Nordln/Customizable-Boot-Camper-Box/20211127_095921_Medium.jpg

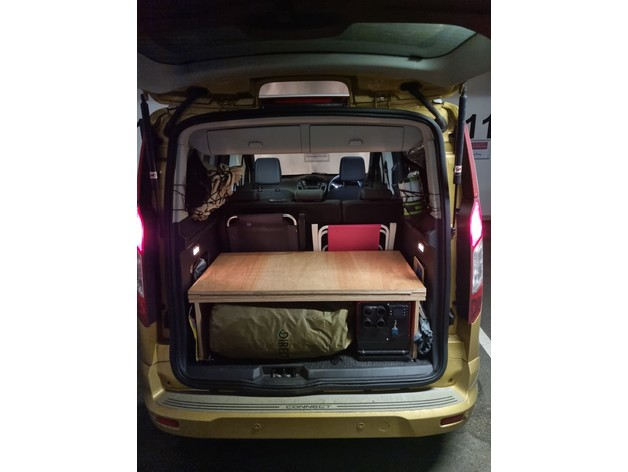
20211127_095921_Medium.jpg
