Nordln/Customizable-Boot-Camper-Box/20211127_100210_Medium.jpg

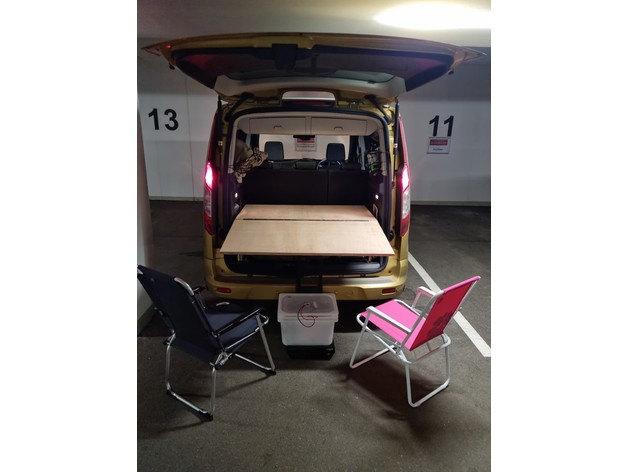
20211127_100210_Medium.jpg
