Nordln/Customizable-Boot-Camper-Box/20211127_100708_Medium.jpg

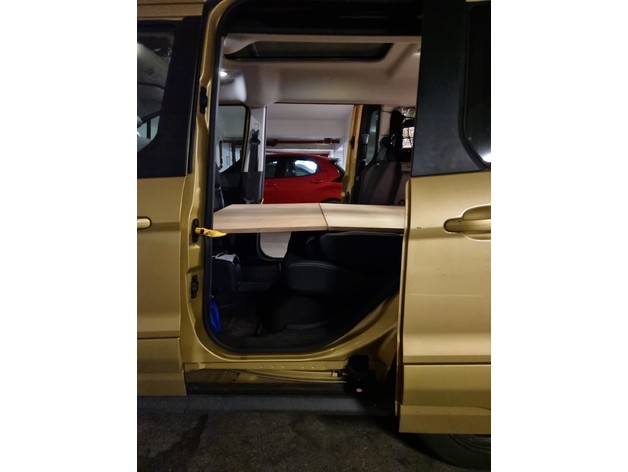
20211127_100708_Medium.jpg
