Nordln/Customizable-Boot-Camper-Box/20220418_084618_sm.jpg

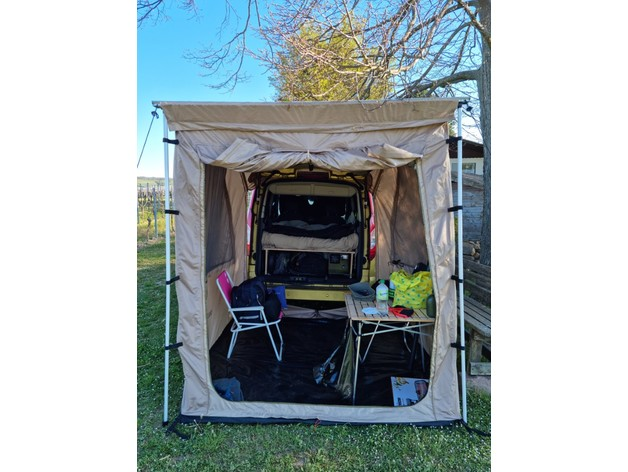
20220418_084618_sm.jpg
