Nordln/Customizable-Boot-Camper-Box/featured_preview_Cutguide.jpg

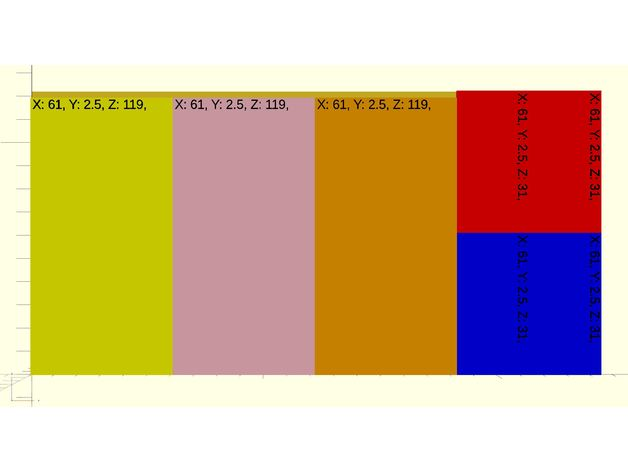
featured_preview_Cutguide.jpg
